RomiFC/Solar-Telescope-Redesign/Research/lecture.2.global.pdf

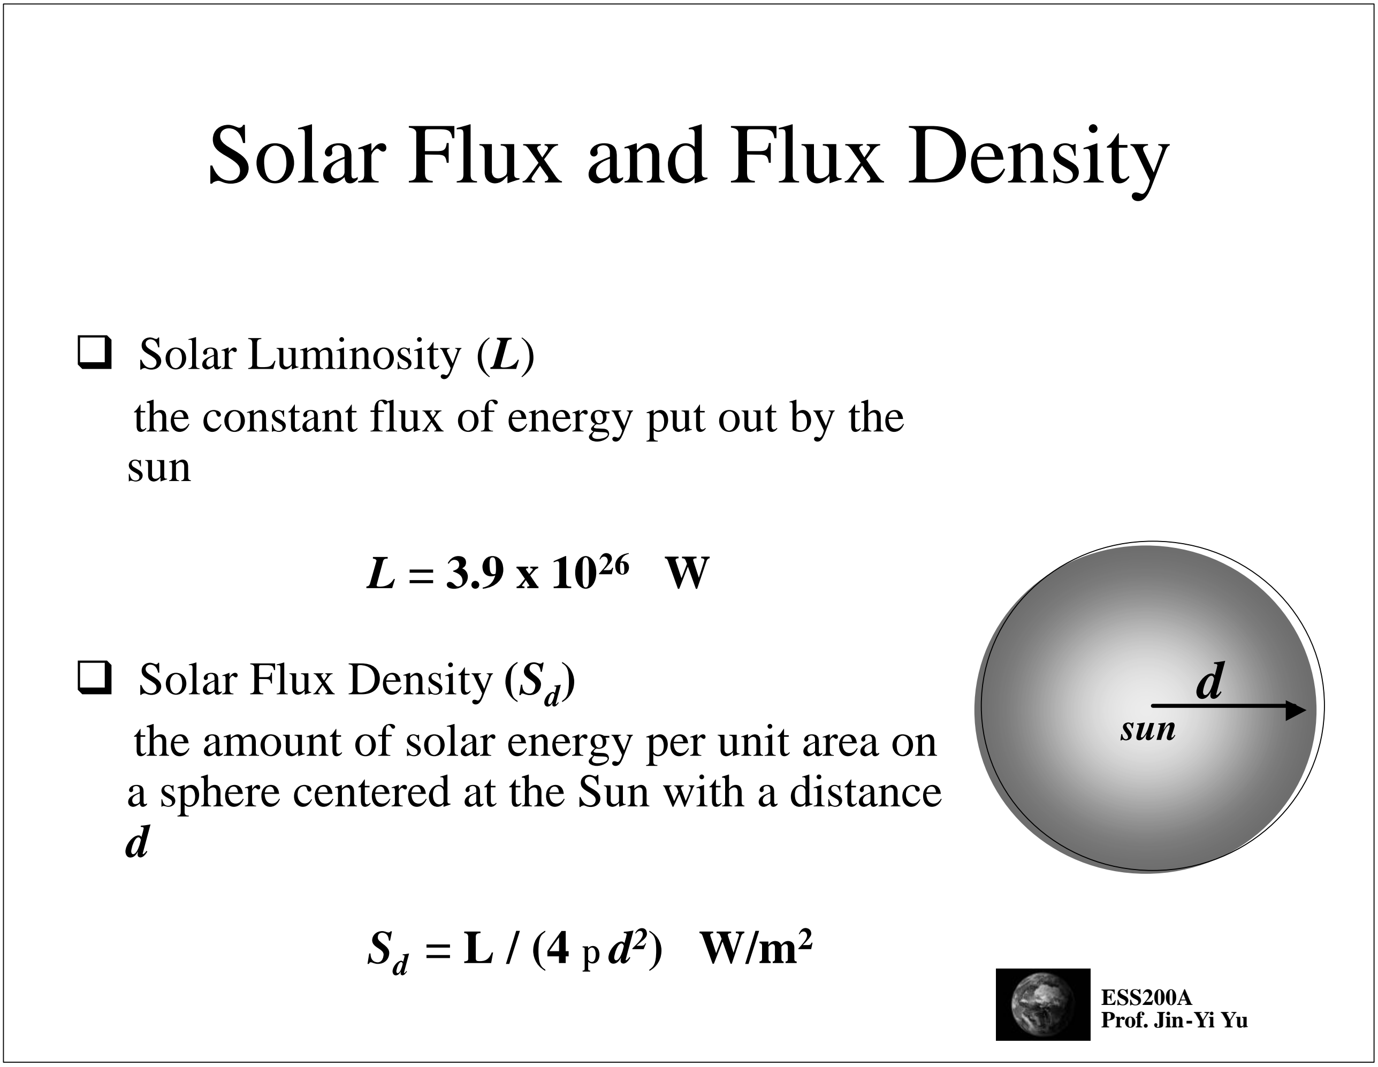
[picture p15: figure]
ESS200A Prof. Jin-Yi Yu; Solar Flux and Flux Density; q Solar Luminosity (L); sun; q Solar Flux Density (Sd )

## the constant flux of energy put out by the

## the amount of solar energy per unit area on a sphere centered at the Sun with a distance

ESS200A
Prof. Jin-Yi Yu

# Solar Flux Density Reaching Earth

## q Solar Constant (S) The solar energy density at the mean distance of Earth from the sun (1.5 x 10

11 m)

## S = L / (4 p d

2
)
= (3.9 x 10

## 26 W) / [4 x 3.14 x (1.5 x 10

### 11 m)

2
]

## = 1370 W/m²

ESS200A
Prof. Jin-Yi Yu

# Solar Energy Incident On the Earth

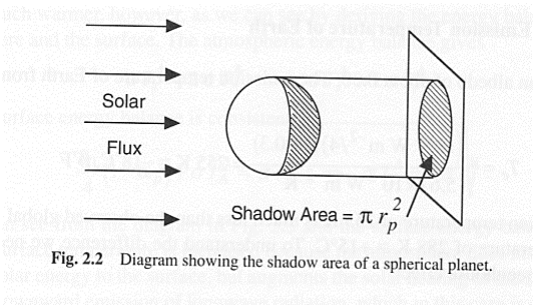
[picture p16: figure]

## q Solar energy incident on the Earth = total amount of solar energy can be absorbed by Earth = (Solar constant) x (Shadow Area) = S x p R²

Earth
ESS200A
Prof. Jin-Yi Yu

# Solar Energy Absorbed by Earth

ß Solar Constant (S)
= solar flux density reaching the Earth = 1370 W/m²

ß Solar energy incident on the Earth = S x the “flat” area of the Earth
= S x π R²
Earth
ß Solar energy absorbed by the Earth
= (received solar flux) – (reflected solar flux) = S π R²
Earth

– S π R²
Earth

x A
= S p R²
Earth

x (1-A)

A is the planetary albedo of the Earth, which is about 0.3.

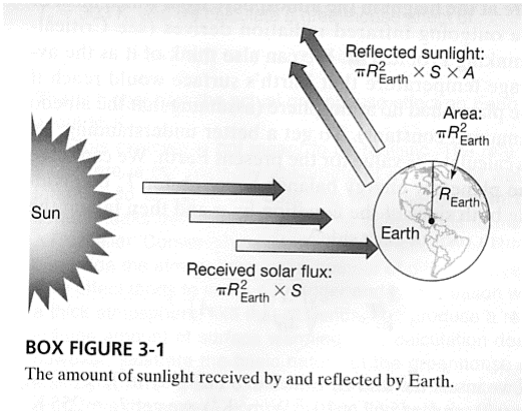
[picture p17: figure]

(from The Earth System)

ESS200A
Prof. Jin-Yi Yu

# What Happens After the Earth Absorbs Solar Energy?

## q The Earth warms up and has to emit radiative energy back to the space to reach a equilibrium

condition.

## q The radiation emitted by the Earth is called “terrestrial radiation” which is assumed to be

like blackbody radiation.

ESS200A
Prof. Jin-Yi Yu

# Blackbody Radiation

## q Blackbody A blackbody is something that emits (or absorbs) electromagnetic radiation with 100% efficiency at

all wavelength.

## q Blackbody Radiation The amount of the radiation emitted by a blackbody depends on the absolute temperature of

the blackbody.

ESS200A
Prof. Jin-Yi Yu

# Energy Emitted from Earth

ß The Stefan-Boltzmann Law
The energy flux emitted by a blackbody is related to the fourth power of the body’s absolute temperature

F = sT⁴ where σ is 5.67x10
-8 W/m²

/K

ß Energy emitted from the Earth
= (blackbody emission) x (total area of Earth) = (σTe

4 ) x (4π R²
Earth

)

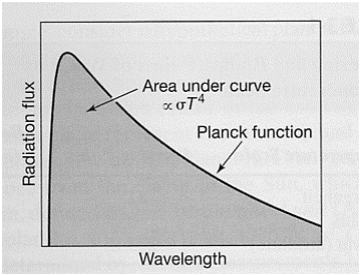
[picture p18: figure]

(from The Earth System)

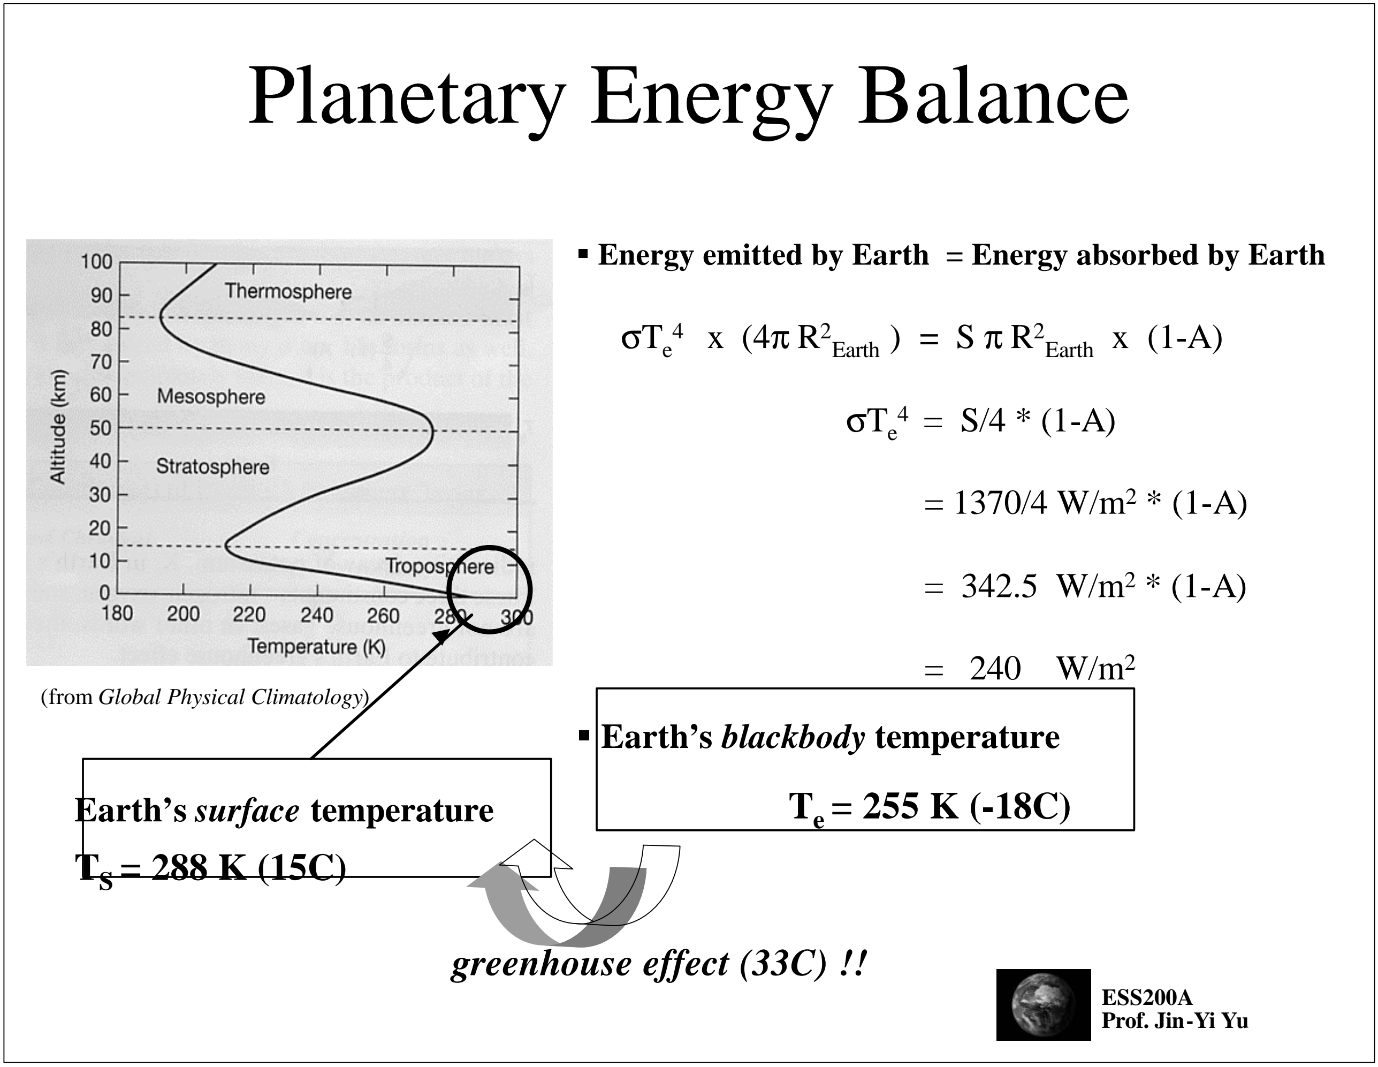
[picture p19: figure]
ESS200A Prof. Jin-Yi Yu; Planetary Energy Balance; σTe; Earth; σTe 4 = S/4 * (1-A); ß Earth’s blackbody temperature; Earth’s surface temperature; greenhouse effect (33C) !!; (from Global Physical Climatology)

ß Energy emitted by Earth = Energy absorbed by Earth

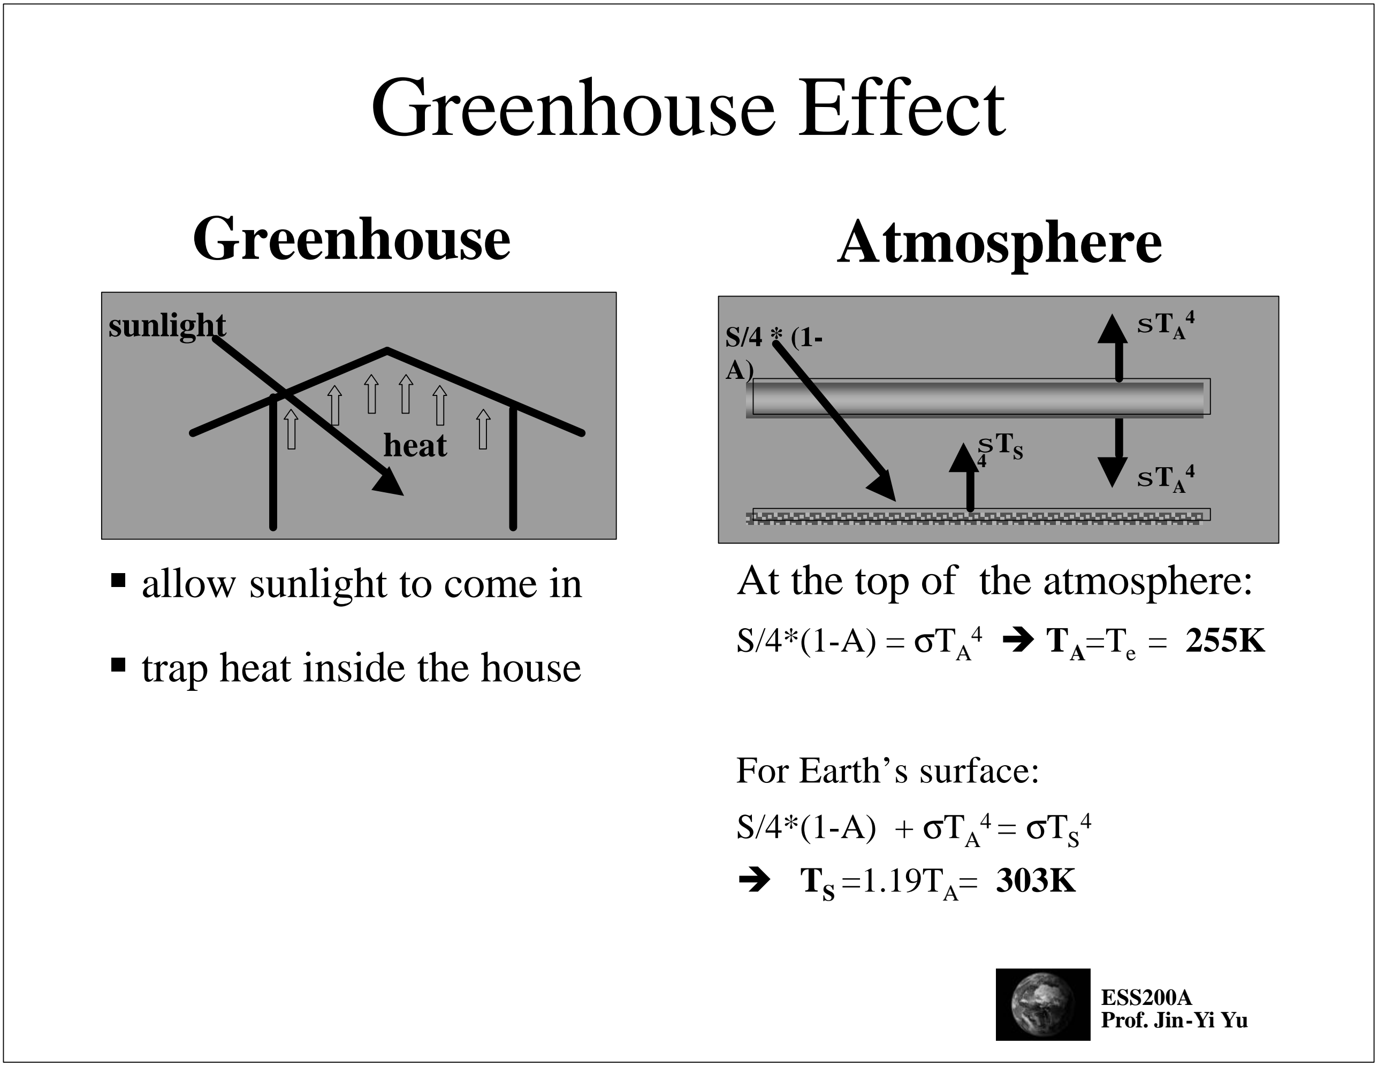
[picture p20: figure]
ESS200A Prof. Jin-Yi Yu; Greenhouse Effect; heat; sunlight; ß allow sunlight to come in; ß trap heat inside the house; Greenhouse; Atmosphere; sTS; sTA 4; At the top of the atmosphere:; S/4*(1-A) = σTA 4 Ë TA=Te = 255K; For Earth’s surface: S/4*(1-A) + σTA; 4 = σTS

ESS200A
Prof. Jin-Yi Yu

## Different Wavelengths of Solar and Earth’s Radiation

Normalized Planck Function | Planck Function

(from The Earth System)

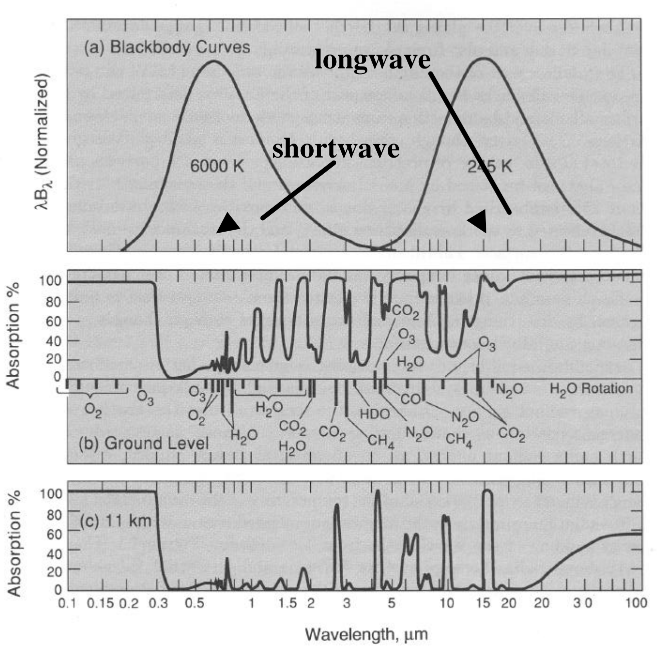
[picture p21: figure]
shortwave; longwave

(from Climate System Modeling)

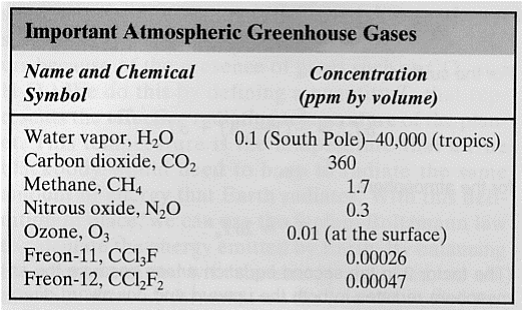
[picture p22: figure]

ESS200A
Prof. Jin-Yi Yu

# Greenhouse Gases

ESS200A
Prof. Jin-Yi Yu

# Where Does the Solar Energy Go?

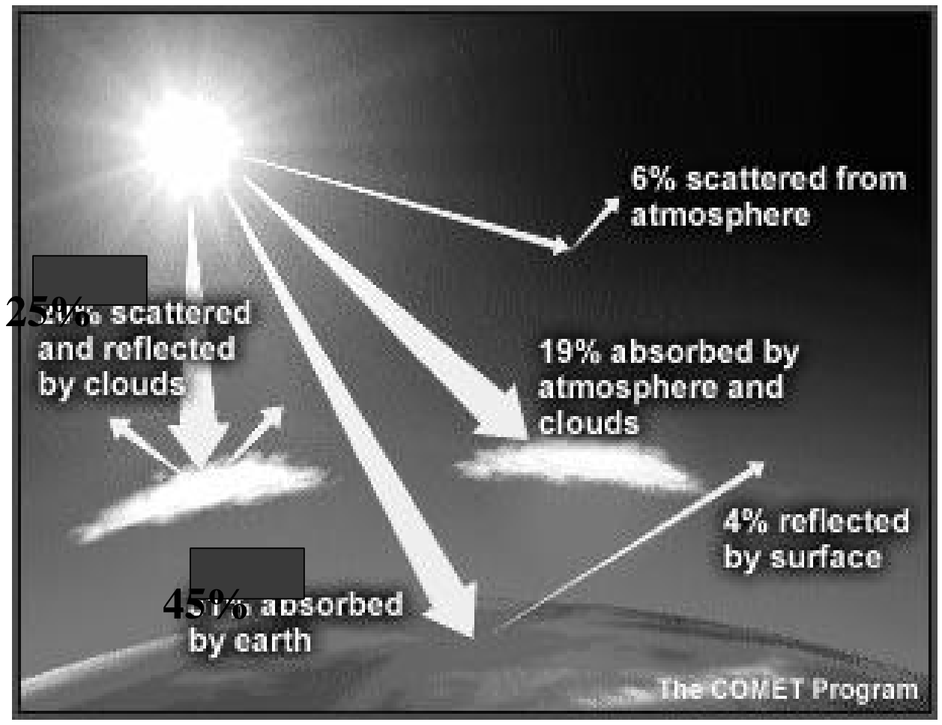
[picture p23: figure]

(from NCAR/COMET website)

## Incoming solar energy (100)

## ß 70% absorbed

45% by Earth’s surface (ocean + land) 25% by the atmosphere and clouds

## ß 30% reflected and scattered back

20% by clouds
6% by the atmosphere
4% by surface

ESS200A
Prof. Jin-Yi Yu

# Where Is Earth’s Radiation Emitted From?

## Radiation back to Space (70 Units)

## ß 70 (units) radiation back to space

66% by the atmosphere
4% by surface (through clear sky)
ß Greenhouse emission (back to surface) 88% (of solar radiation)

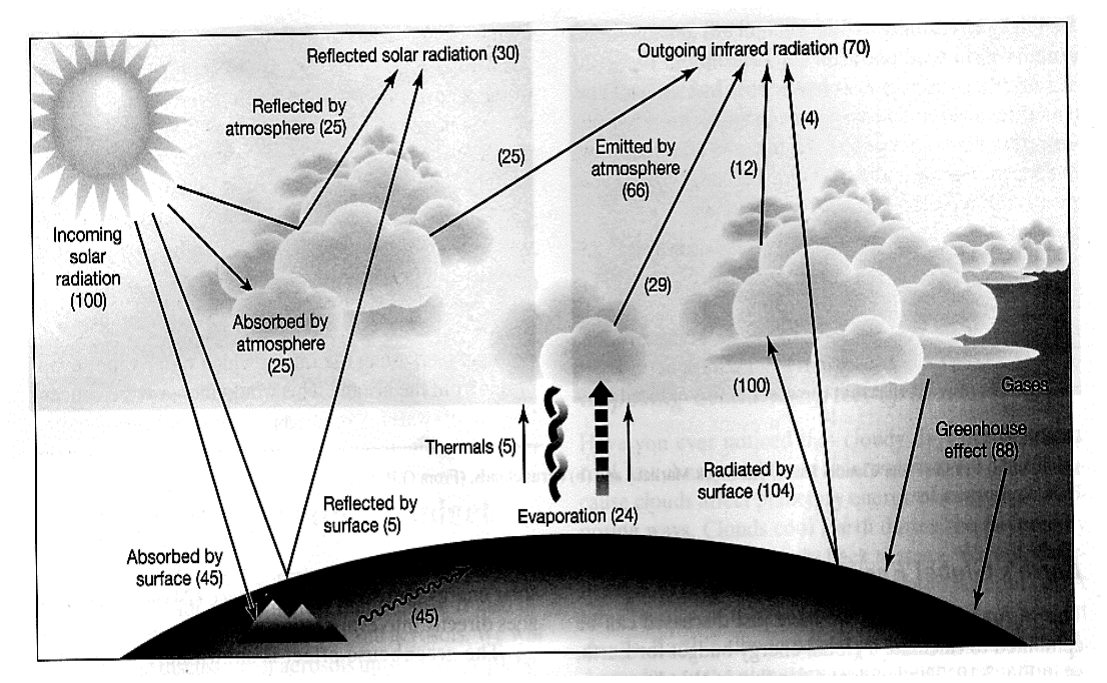
[picture p24: figure]

(from The Earth System)

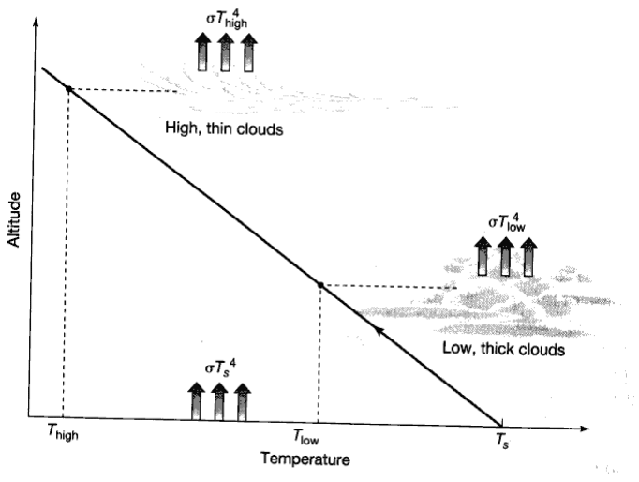
[picture p25: figure]

ESS200A
Prof. Jin-Yi Yu

# Important Roles of Clouds In Global Climate

(from The Earth System)

ESS200A
Prof. Jin-Yi Yu

# Polarward Energy Transport

Annual-Mean Radiative Energy | Polarward Heat Flux

Polarward heat flux is needed to transport radiative energy from the tropics to higher latitudes

The atmosphere dominates the polarward heat transport at middle and high latitudes. The ocean dominates the transport at lower latitudes.

(1 petaWatts = 10¹⁵ W)

(figures from Global Physical Climatology)

ESS200A
Prof. Jin-Yi Yu

## How Do Atmosphere and Ocean Transport Heat?

Atmospheric Circulation | Ocean Circulation

(bottom from USGCRP)

(from USA Today)

(top from The Earth System)
